liveboxandy/ZX-Max-PlusD-Issue-1/Step/PJ-322.step

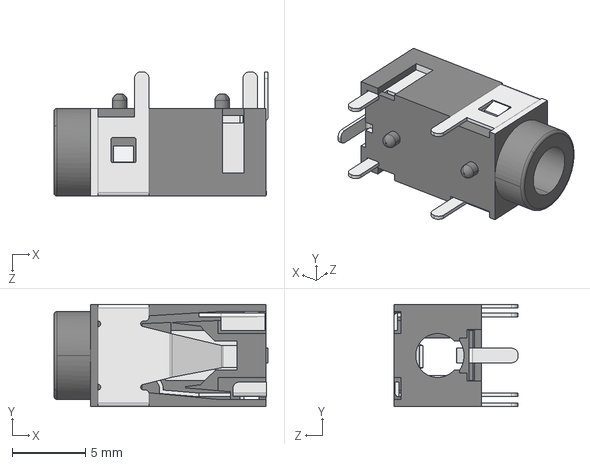
[picture p17: CAD file, 2026-02-05]
Step/PJ-322.step
14.6 x 7.00 x 8.50 mm
