liveboxandy/ZX-Max-PlusD-Issue-1/Step/PJ-002A.step

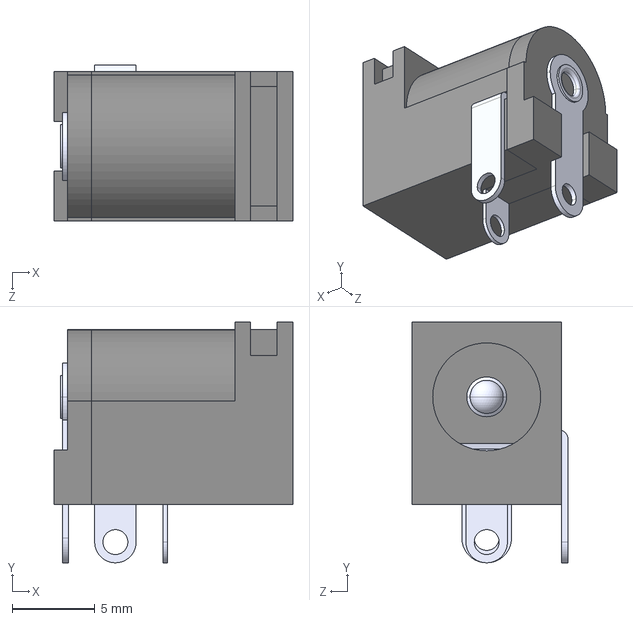
[picture p18: CAD file, 2026-02-05]
Step/PJ-002A.step
14.4 x 14.5 x 9.40 mm
