liveboxandy/ZX-Max-PlusD-Issue-1/Step/DIP-28_W15.24mm_Socket.step

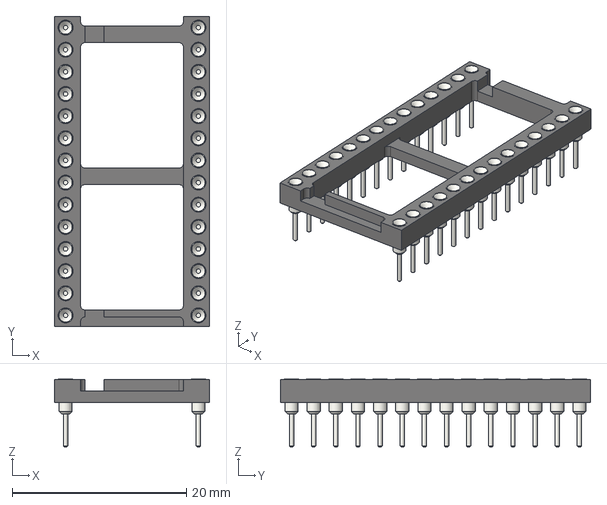
[picture p19: CAD file, 2026-02-05]
Step/DIP-28_W15.24mm_Socket.step
17.8 x 35.6 x 7.79 mm
