liveboxandy/ZX-Max-PlusD-Issue-1/Step/DIP-16_W7.62mm.step

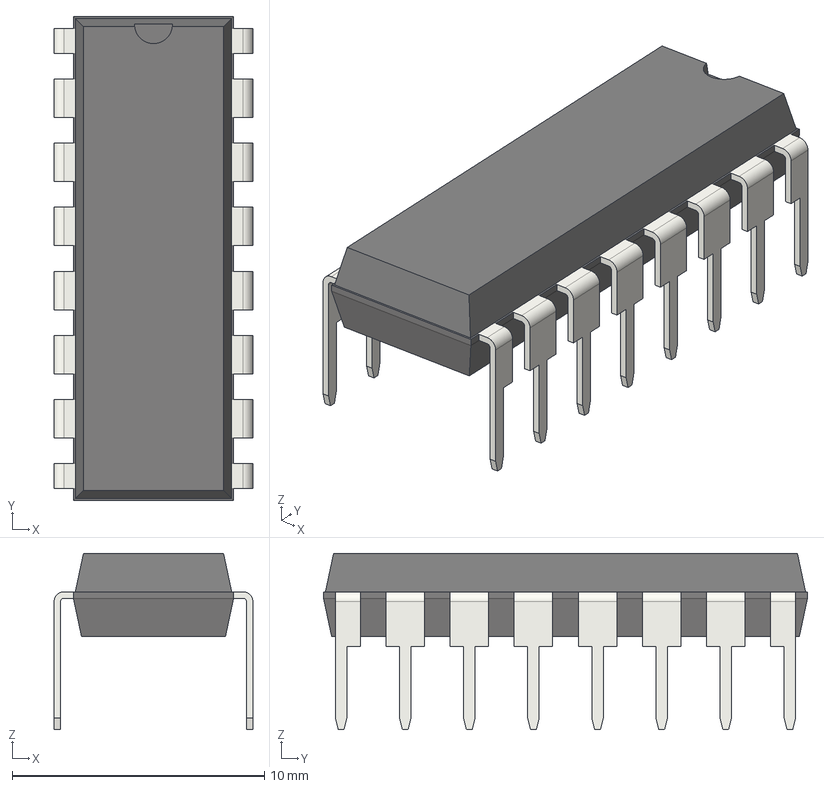
[picture p20: CAD file, 2026-02-05]
Step/DIP-16_W7.62mm.step
7.87 x 19.2 x 6.98 mm
