liveboxandy/ZX-Max-PlusD-Issue-1/Step/DIP-28_W15.24mm.step

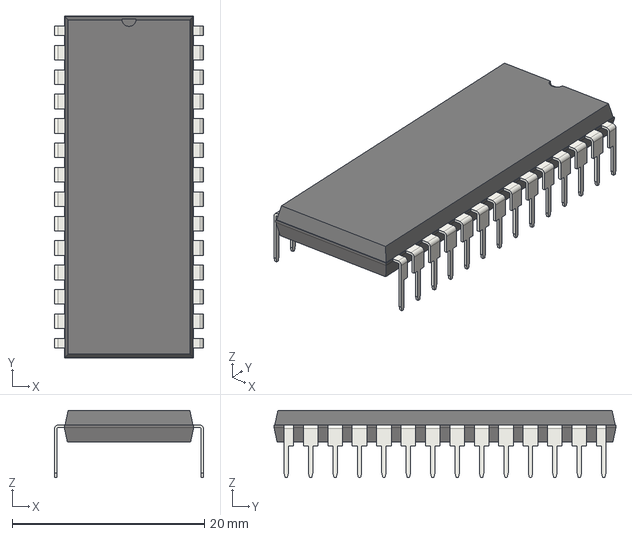
[picture p21: CAD file, 2026-02-05]
Step/DIP-28_W15.24mm.step
15.5 x 35.6 x 6.98 mm
