liveboxandy/ZX-Max-PlusD-Issue-1/Step/Connector Pin-Pin 5x2 10129381-910002BLF.step

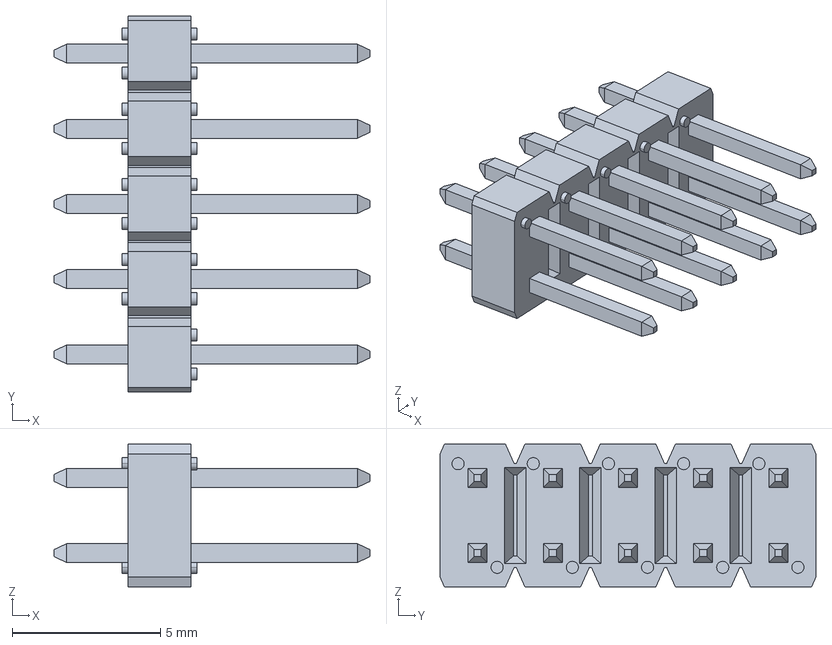
[picture p22: CAD file, 2026-02-05]
Step/Connector Pin-Pin 5x2 10129381-910002BLF.step
10.7 x 12.7 x 4.83 mm
