liveboxandy/ZX-Max-PlusD-Issue-1/Step/ADI724JRZ RW_16_ADI.step

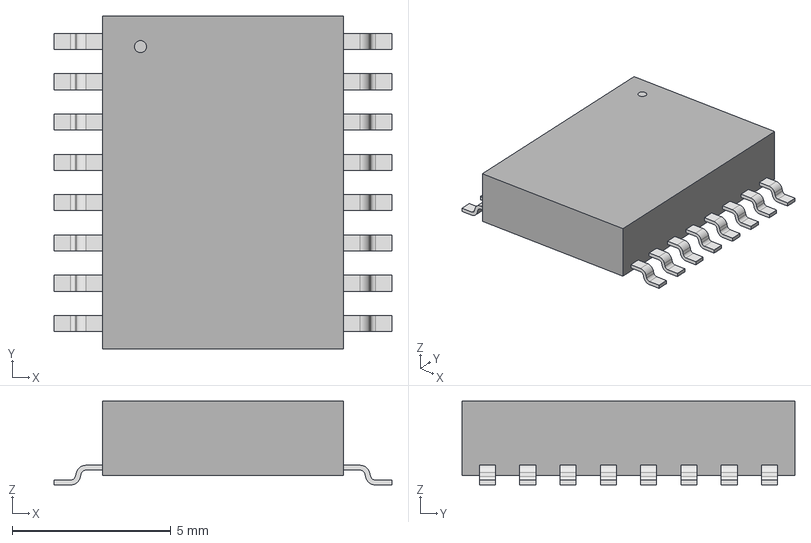
[picture p23: CAD file, 2026-02-05]
Step/ADI724JRZ RW_16_ADI.step
10.6 x 10.5 x 2.64 mm
