liveboxandy/ZX-Max-PlusD-Issue-1/Step/9Pin MiniDIN KMDGX-9S-BS-1_A1.IGS

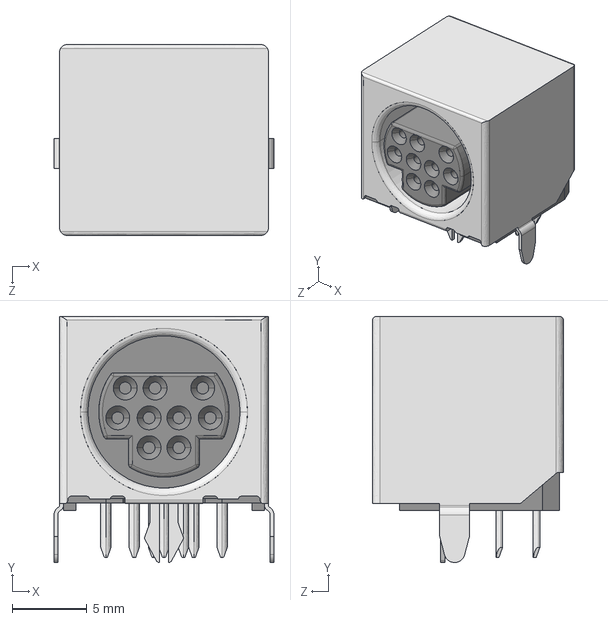
[picture p24: CAD file, 2026-02-05]
Step/9Pin MiniDIN KMDGX-9S-BS-1_A1.IGS
14.8 x 16.5 x 12.8 mm
