liveboxandy/ZX-Max-PlusD-Issue-1/Step/DIP-18_W7.62mm_Socket.step

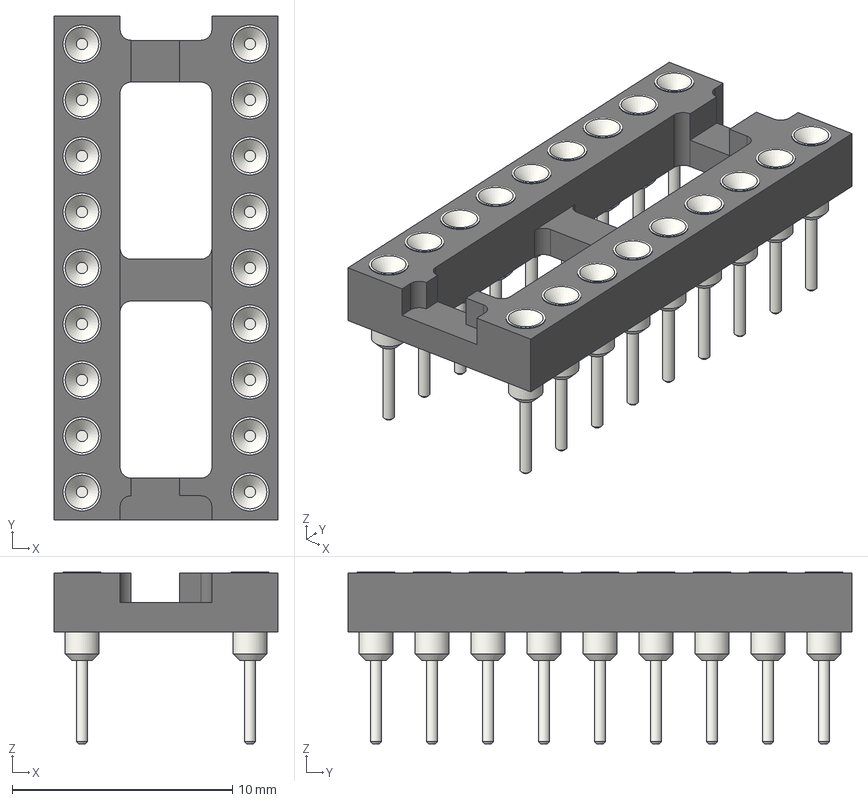
[picture p25: CAD file, 2026-02-05]
Step/DIP-18_W7.62mm_Socket.step
10.2 x 22.9 x 7.79 mm
