liveboxandy/ZX-Max-PlusD-Issue-1/Step/Oscillator 4 Pin 8Mhz ECS-2100A-080.step

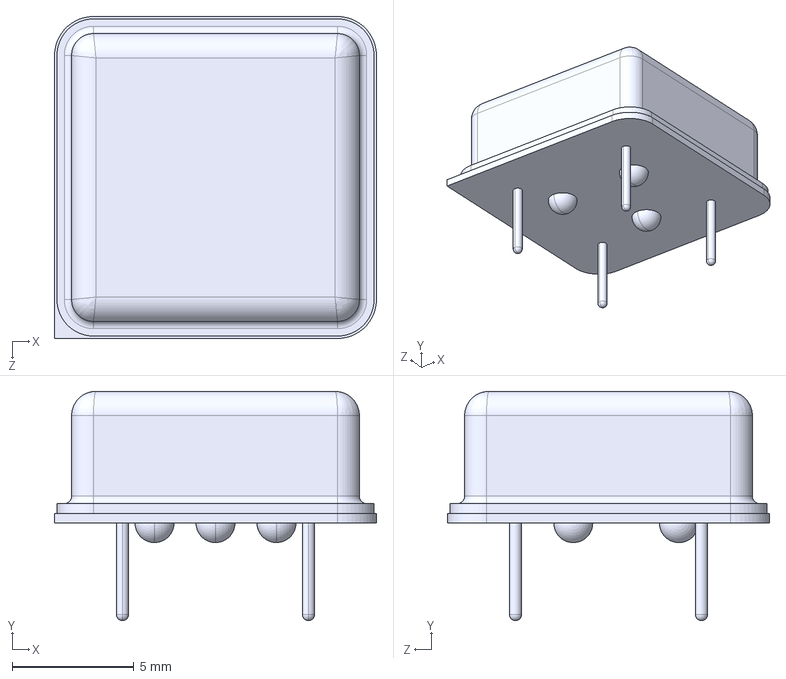
[picture p26: CAD file, 2026-02-05]
Step/Oscillator 4 Pin 8Mhz ECS-2100A-080.step
13.2 x 9.40 x 13.2 mm
