liveboxandy/ZX-Max-PlusD-Issue-1/Step/Capacitor 22uF 16V 5x7 EEAGA1C220H.step

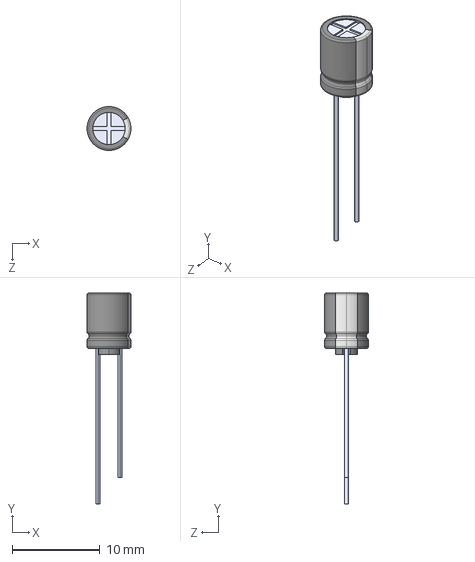
[picture p27: CAD file, 2026-02-05]
Step/Capacitor 22uF 16V 5x7 EEAGA1C220H.step
5.00 x 24.0 x 4.99 mm
