liveboxandy/ZX-Max-PlusD-Issue-1/Step/RNET 10K 6Pin 4606X-101-103LF.STEP

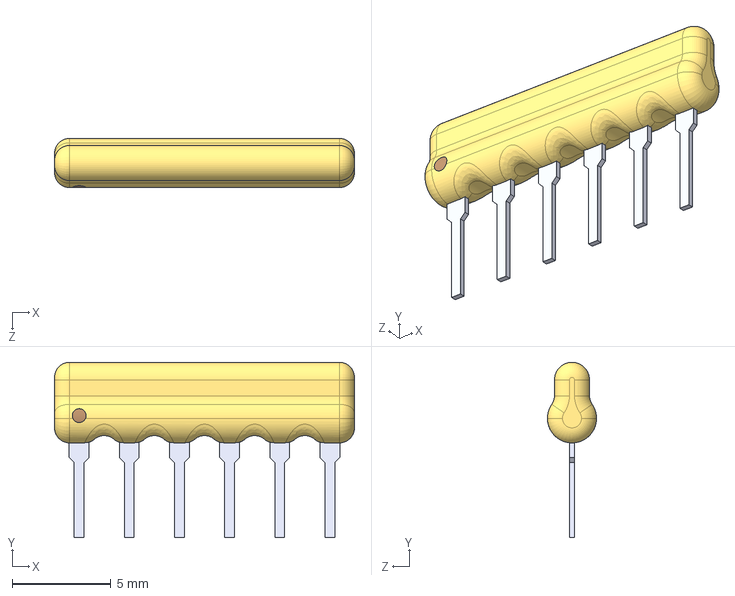
[picture p28: CAD file, 2026-02-05]
Step/RNET 10K 6Pin 4606X-101-103LF.STEP
15.2 x 8.88 x 2.49 mm
