liveboxandy/ZX-Max-PlusD-Issue-1/Step/QFN-40 (6x6x0.9).step

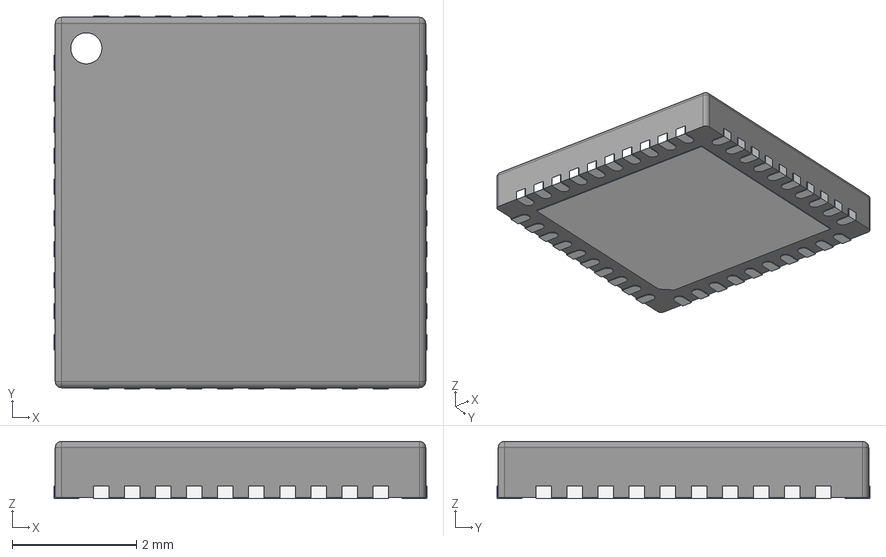
[picture p29: CAD file, 2026-02-05]
Step/QFN-40 (6x6x0.9).step
6.00 x 6.00 x 0.92 mm
