liveboxandy/ZX-Max-PlusD-Issue-1/Step/Capacitor 100nF 50V MLCC K104Z15Y5VF5TL2.stp

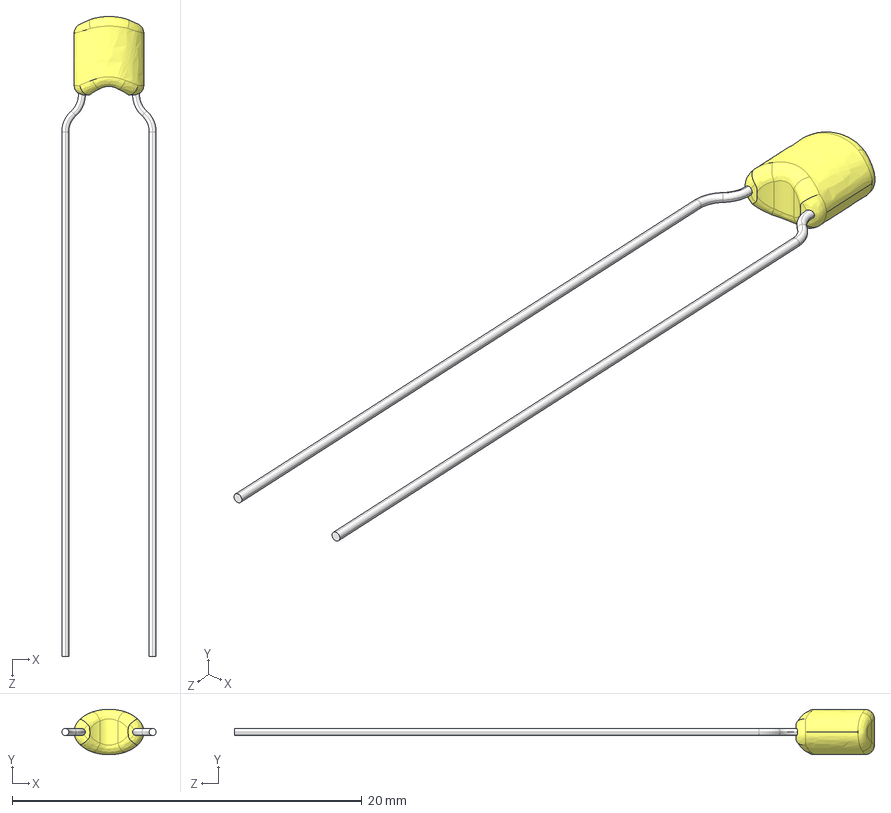
[picture p30: CAD file, 2026-02-05]
Step/Capacitor 100nF 50V MLCC K104Z15Y5VF5TL2.stp
5.40 x 2.60 x 36.6 mm
