liveboxandy/ZX-Max-PlusD-Issue-1/Step/R-78E5.0-1.0.step

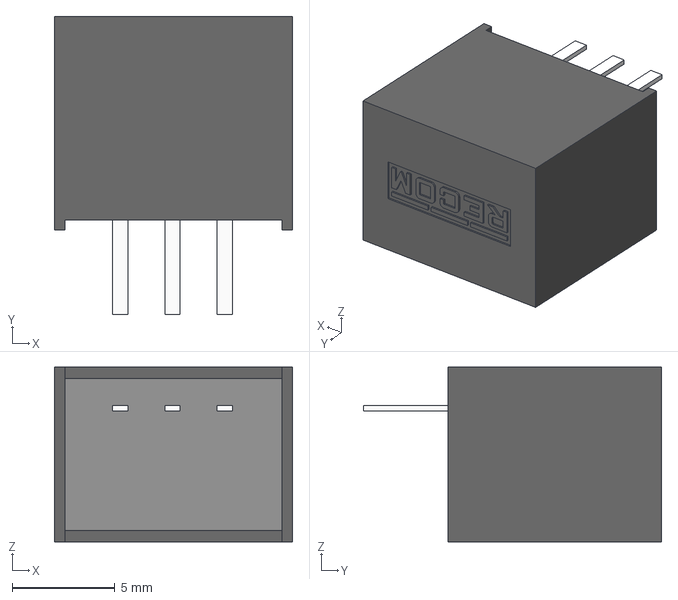
[picture p31: CAD file, 2026-02-05]
Step/R-78E5.0-1.0.step
11.6 x 14.5 x 8.50 mm
