liveboxandy/ZX-Max-PlusD-Issue-1/Step/Transistor BC548BTA.stp

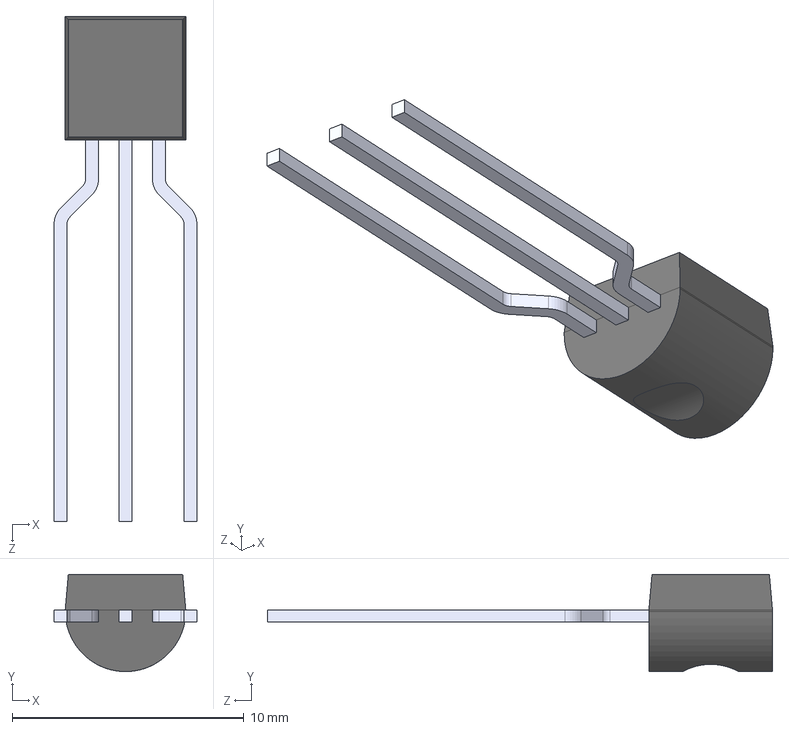
[picture p32: CAD file, 2026-02-05]
Step/Transistor BC548BTA.stp
6.16 x 4.19 x 21.8 mm
