liveboxandy/ZX-Max-PlusD-Issue-1/Step/Connector 5 Way Keyboard CONN_5-520315-5.stp

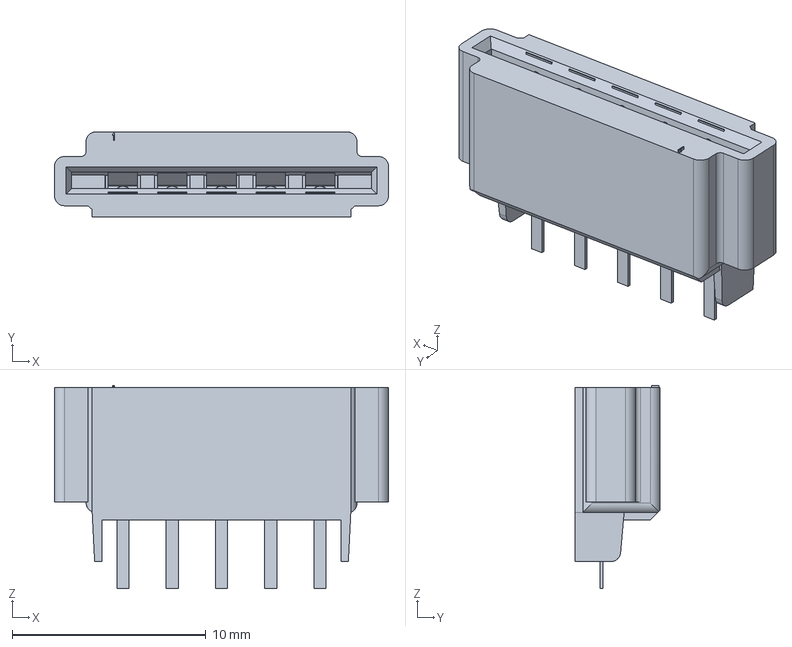
[picture p33: CAD file, 2026-02-05]
Step/Connector 5 Way Keyboard CONN_5-520315-5.stp
17.2 x 4.39 x 10.5 mm
