liveboxandy/ZX-Max-PlusD-Issue-1/Step/Header 17x2 RA c-5103311-7-b-3d.stp

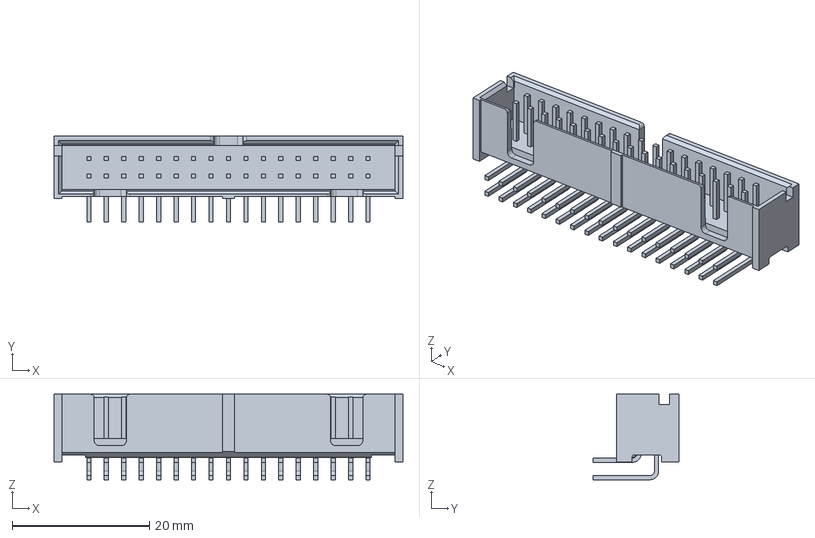
[picture p34: CAD file, 2026-02-05]
Step/Header 17x2 RA c-5103311-7-b-3d.stp
50.8 x 12.6 x 12.5 mm
