liveboxandy/ZX-Max-PlusD-Issue-1/Step/Resistor.08.88.step

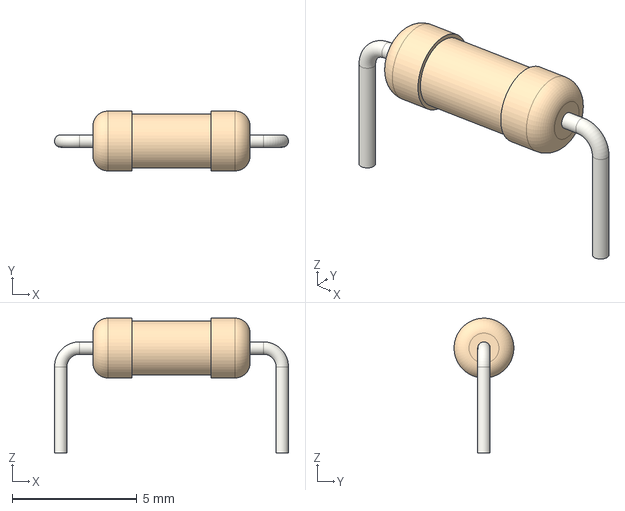
[picture p35: CAD file, 2026-02-05]
Step/Resistor.08.88.step
9.38 x 2.40 x 5.40 mm
