liveboxandy/ZX-Max-PlusD-Issue-1/Step/DIP-14_W7.62mm_Socket.step

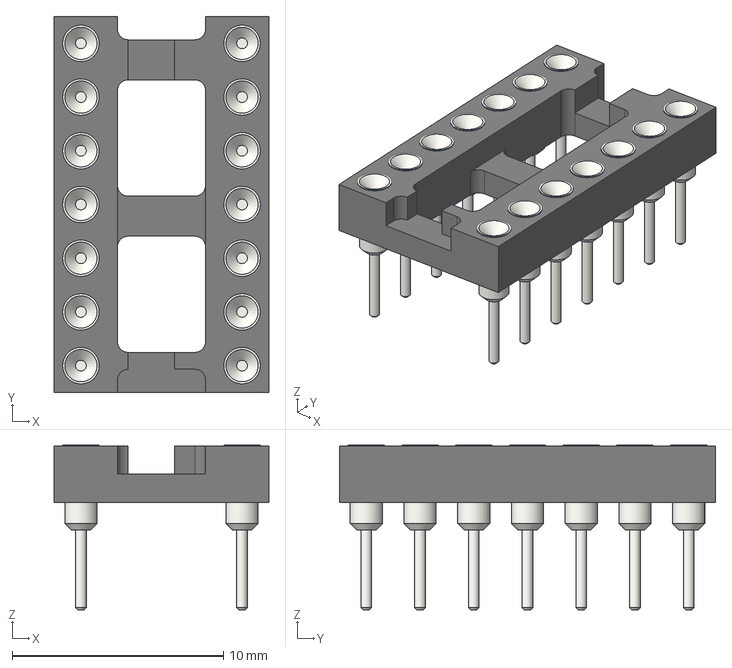
[picture p36: CAD file, 2026-02-05]
Step/DIP-14_W7.62mm_Socket.step
10.2 x 17.8 x 7.79 mm
