liveboxandy/ZX-Max-PlusD-Issue-1/Step/IND_BOURNS_RLB0608.step

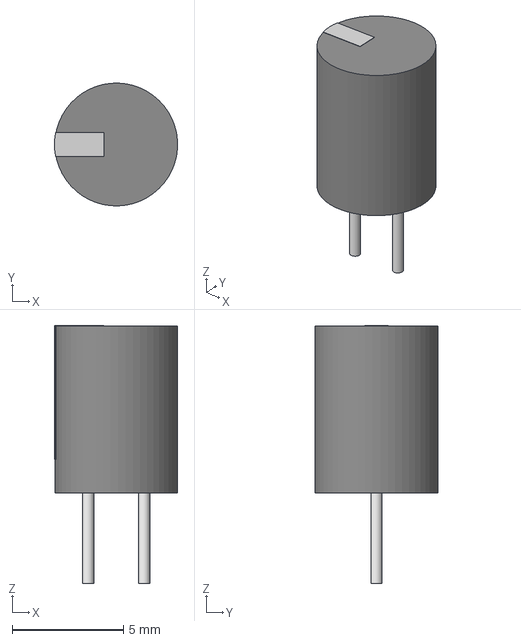
[picture p37: CAD file, 2026-02-05]
Step/IND_BOURNS_RLB0608.step
5.52 x 5.51 x 11.6 mm
