liveboxandy/ZX-Max-PlusD-Issue-1/Step/Crystal TH 2 Pin.stp

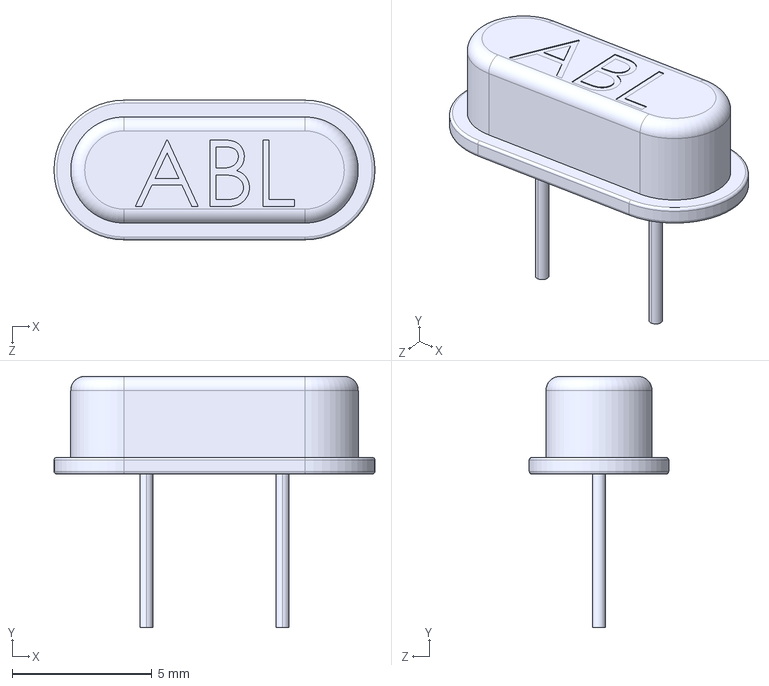
[picture p38: CAD file, 2026-02-05]
Step/Crystal TH 2 Pin.stp
11.5 x 9.00 x 5.00 mm
