liveboxandy/ZX-Max-PlusD-Issue-1/Step/9Pin D MRA Assmannn A-DS_09_A_KG-T4S.step

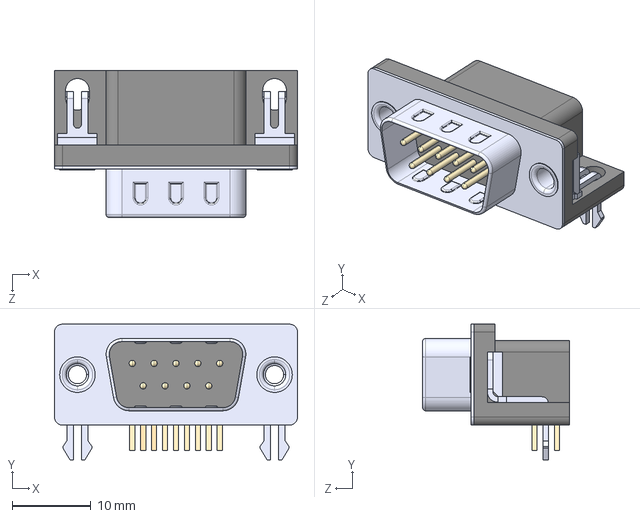
[picture p40: CAD file, 2026-02-05]
Step/9Pin D MRA Assmannn A-DS_09_A_KG-T4S.step
30.8 x 17.2 x 18.6 mm
