liveboxandy/ZX-Max-PlusD-Issue-1/Step/Header 2x2 PH2-04-UA.STEP

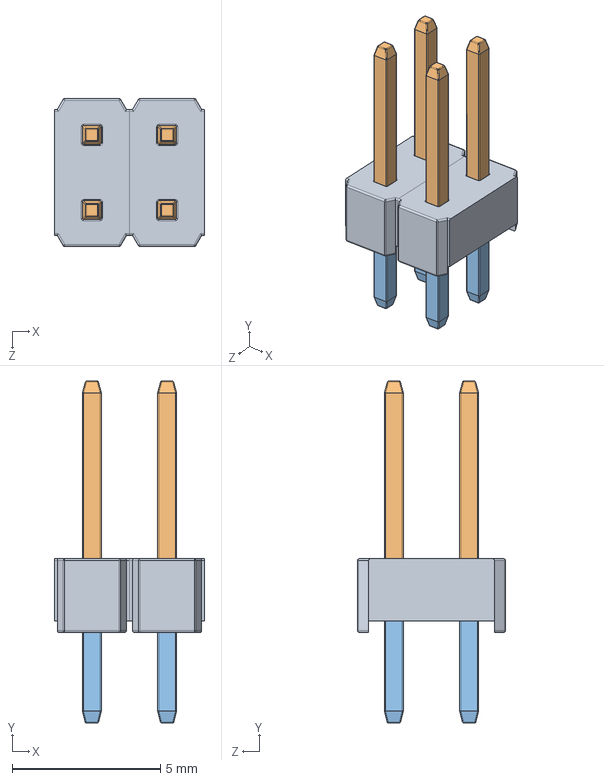
[picture p41: CAD file, 2026-02-05]
Step/Header 2x2 PH2-04-UA.STEP
5.08 x 11.6 x 5.00 mm
