liveboxandy/ZX-Max-PlusD-Issue-1/Step/Voltage Regulator AZ1117IH-3.3TRG1.step

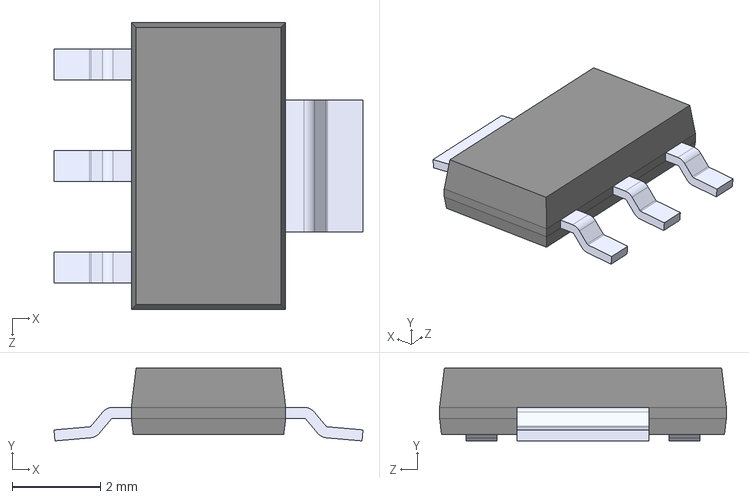
[picture p42: CAD file, 2026-02-05]
Step/Voltage Regulator AZ1117IH-3.3TRG1.step
7.00 x 1.65 x 6.50 mm
