liveboxandy/ZX-Max-PlusD-Issue-1/Step/PLCC-84-AT.stp

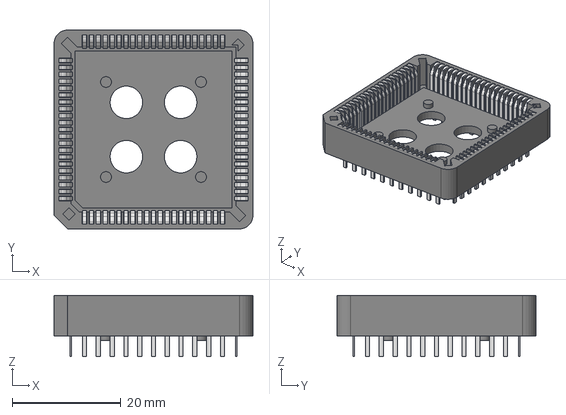
[picture p44: CAD file, 2026-02-05]
Step/PLCC-84-AT.stp
36.7 x 36.7 x 11.3 mm
