liveboxandy/ZX-Max-PlusD-Issue-1/Step/DIP-24_W7.62mm_Socket.step

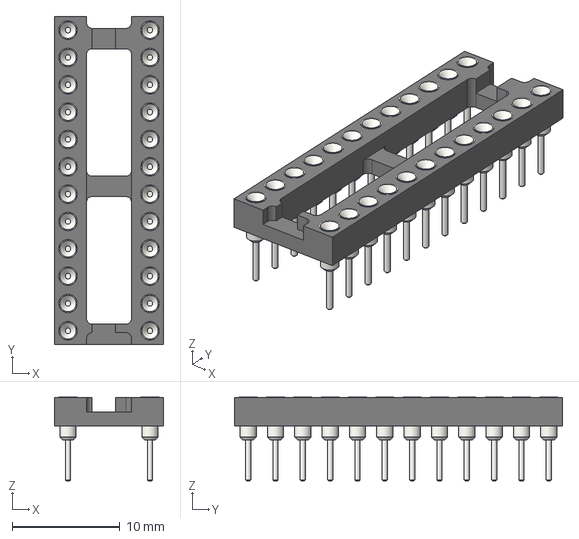
[picture p45: CAD file, 2026-02-05]
Step/DIP-24_W7.62mm_Socket.step
10.2 x 30.5 x 7.79 mm
