liveboxandy/ZX-Max-PlusD-Issue-1/Step/Crystal_HC49-4H_Vertical.step

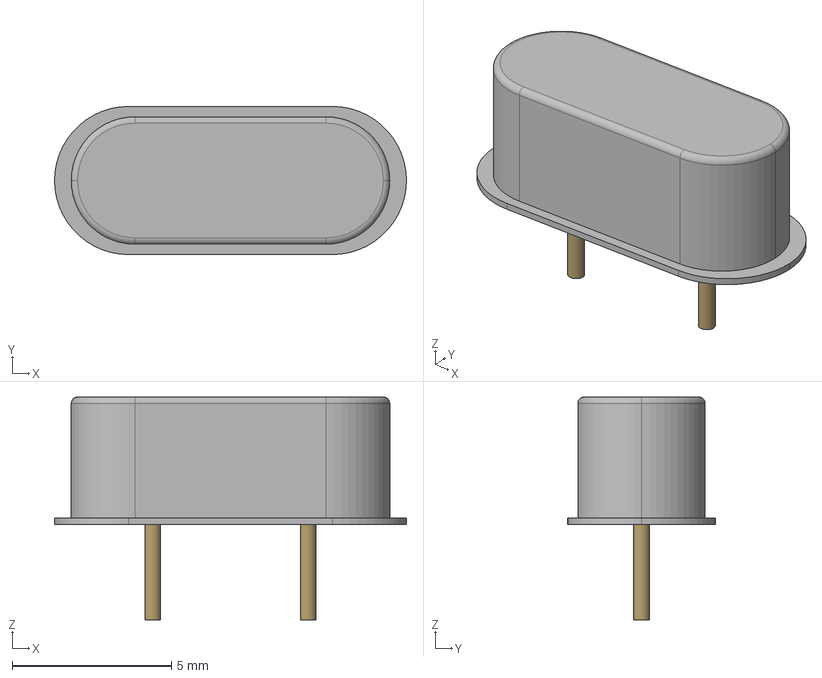
[picture p47: CAD file, 2026-02-05]
Step/Crystal_HC49-4H_Vertical.step
11.1 x 4.65 x 7.00 mm
