liveboxandy/ZX-Max-PlusD-Issue-1/Step/DIP-32_W15.24mm.step

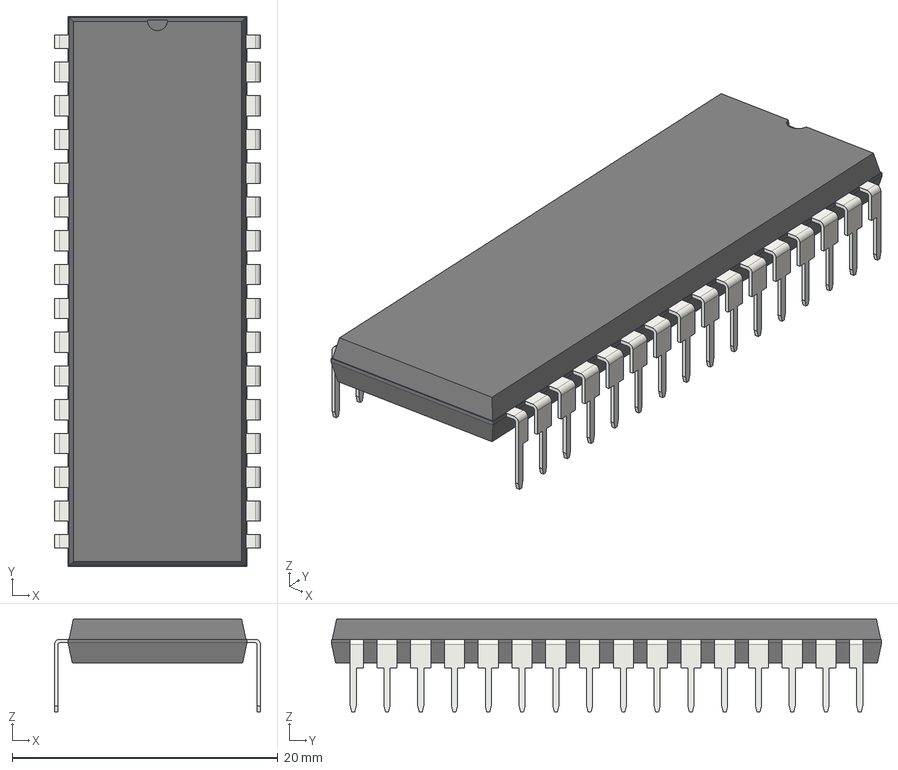
[picture p48: CAD file, 2026-02-05]
Step/DIP-32_W15.24mm.step
15.5 x 41.4 x 6.98 mm
