liveboxandy/ZX-Max-PlusD-Issue-1/Step/Capacitor 10uF 25V ECA-1EM100B.stp

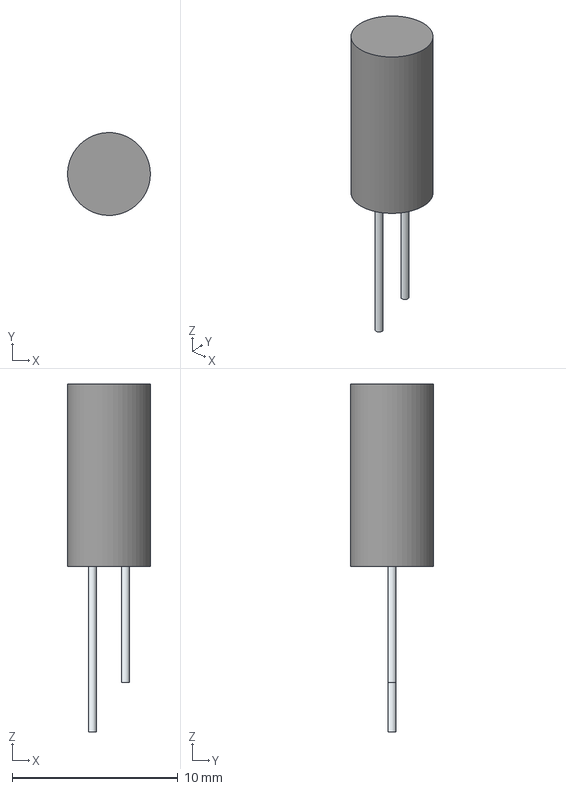
[picture p49: CAD file, 2026-02-05]
Step/Capacitor 10uF 25V ECA-1EM100B.stp
5.00 x 5.00 x 21.0 mm
SimpleBody
Pin1
Pin2
