liveboxandy/ZX-Max-PlusD-Issue-1/Step/Connector Pin-Pin 1x2 M20-9990246.step

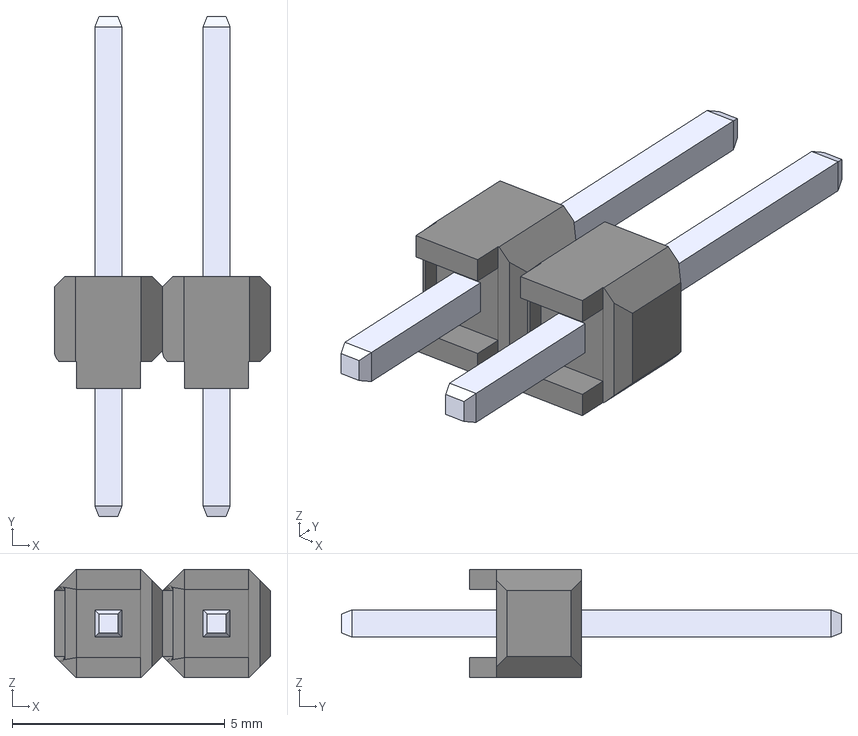
[picture p50: CAD file, 2026-02-05]
Step/Connector Pin-Pin 1x2 M20-9990246.step
5.08 x 11.7 x 2.54 mm
