liveboxandy/ZX-Max-PlusD-Issue-1/Step/Connector 8 Way Keyboard CONN_5-520315-8_TYC.stp

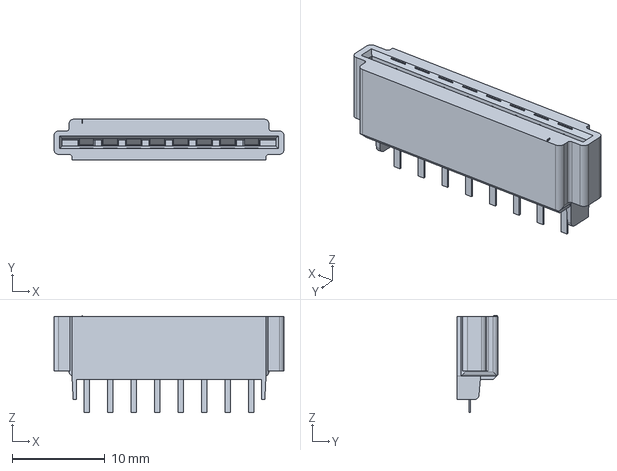
[picture p52: CAD file, 2026-02-05]
Step/Connector 8 Way Keyboard CONN_5-520315-8_TYC.stp
24.8 x 4.39 x 10.5 mm
